eksdat/BoviSense/figuras/fig3_estagio_potencia.png

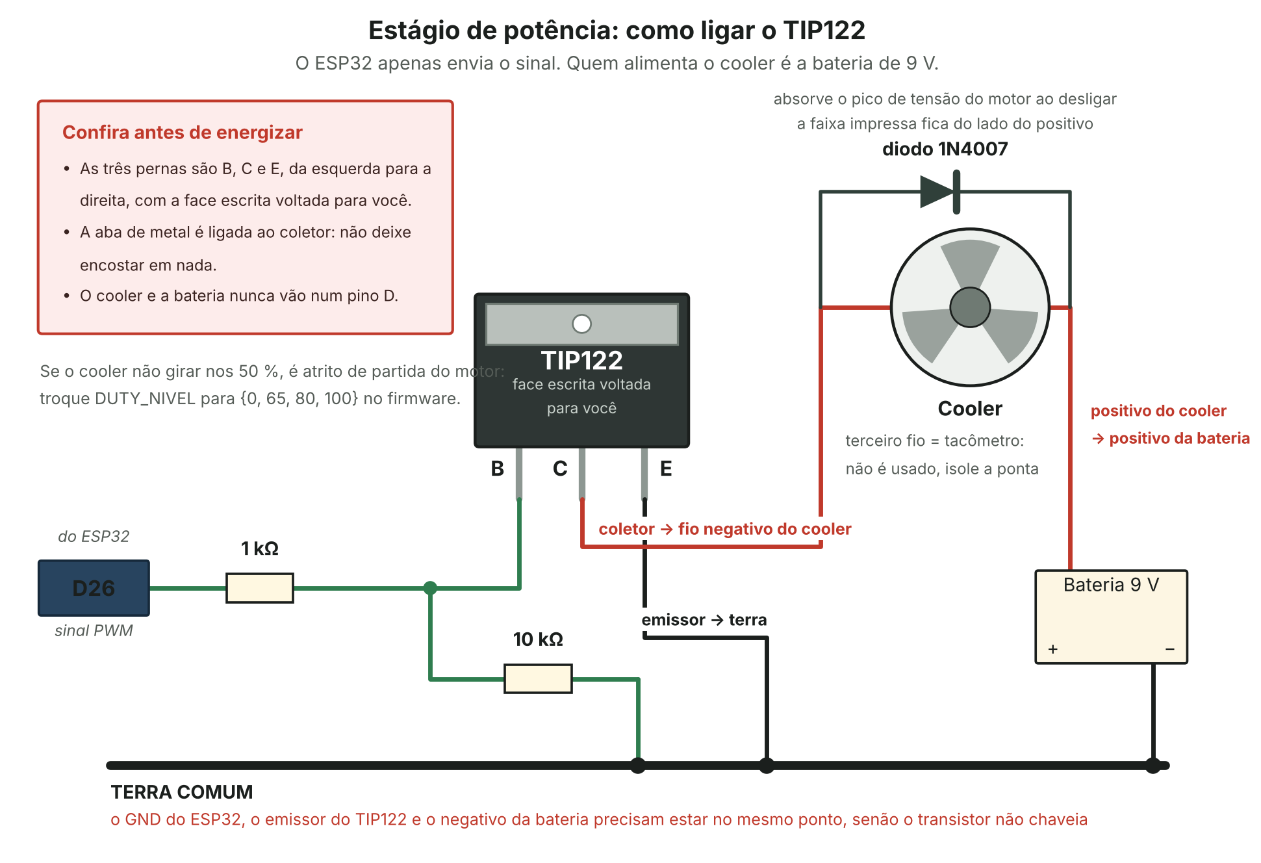
figuras/fig3_estagio_potencia.png
