eksdat/BoviSense/firmware/BoviSense.ino

/*
 * BoviSense — monitoramento ambiental e ventilação adaptativa para bovinos
 *
 * Abas: BoviSense.ino (esta, só instruções) | bovisense.cpp (programa) | segredos.h (senhas)
 * Placa: "ESP32 Dev Module". Monitor Serial: 115200.
 * Bibliotecas: Adafruit SSD1306, Adafruit GFX Library, DHT sensor library,
 *              Adafruit Unified Sensor, ArduinoJson (7.x)
 * O código fica no .cpp de propósito: a IDE não pré-processa .cpp, o que evita
 * erros com a página HTML embutida. Veja LEIA-ME.md.
 */
